VirajSanghani/vara/electronics/vara_cartridge.kicad_sch

## KiCad design electronics/vara_cartridge.kicad_sch (2026-06-03)

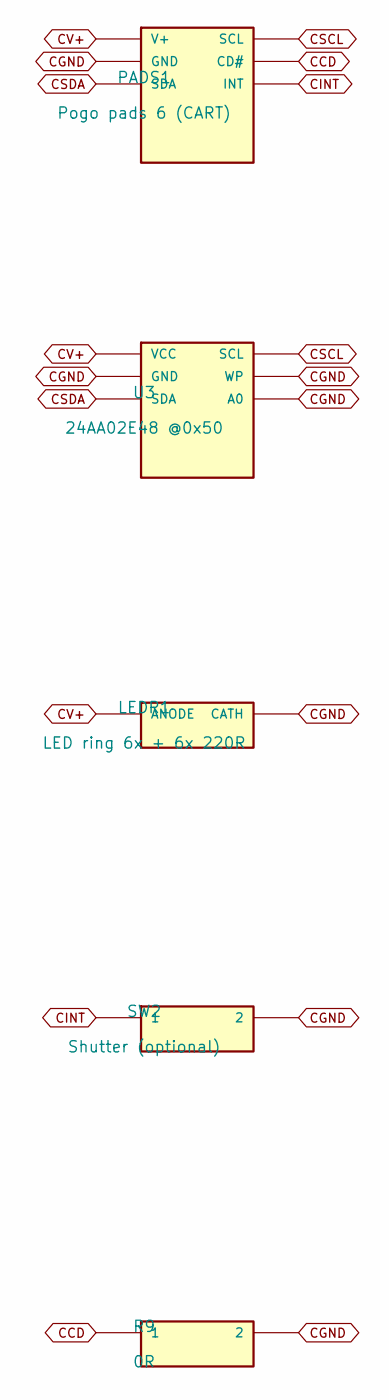
[picture p17: schematic vara_cartridge.kicad_sch]

Parts:
LEDR1: LED ring 6x + 6x 220R
PADS1: Pogo pads 6 (CART)
R9: 0R; R_0402_1005Metric
SW2: Shutter (optional)
U3: 24AA02E48 @0x50; SOT-23-6

Connections:
CCD: PADS1.5 (CD#), R9.1
CGND: LEDR1.K (CATH), PADS1.2 (GND), R9.2, SW2.2, U3.A0, U3.GND, U3.WP
CINT: PADS1.6 (INT), SW2.1
CSCL: PADS1.4 (SCL), U3.SCL
CSDA: PADS1.3 (SDA), U3.SDA
CV+: LEDR1.A (ANODE), PADS1.1 (V+), U3.VCC
