VirajSanghani/vara/electronics/vara_core.kicad_sch

## KiCad design electronics/vara_core.kicad_sch (2026-06-03)

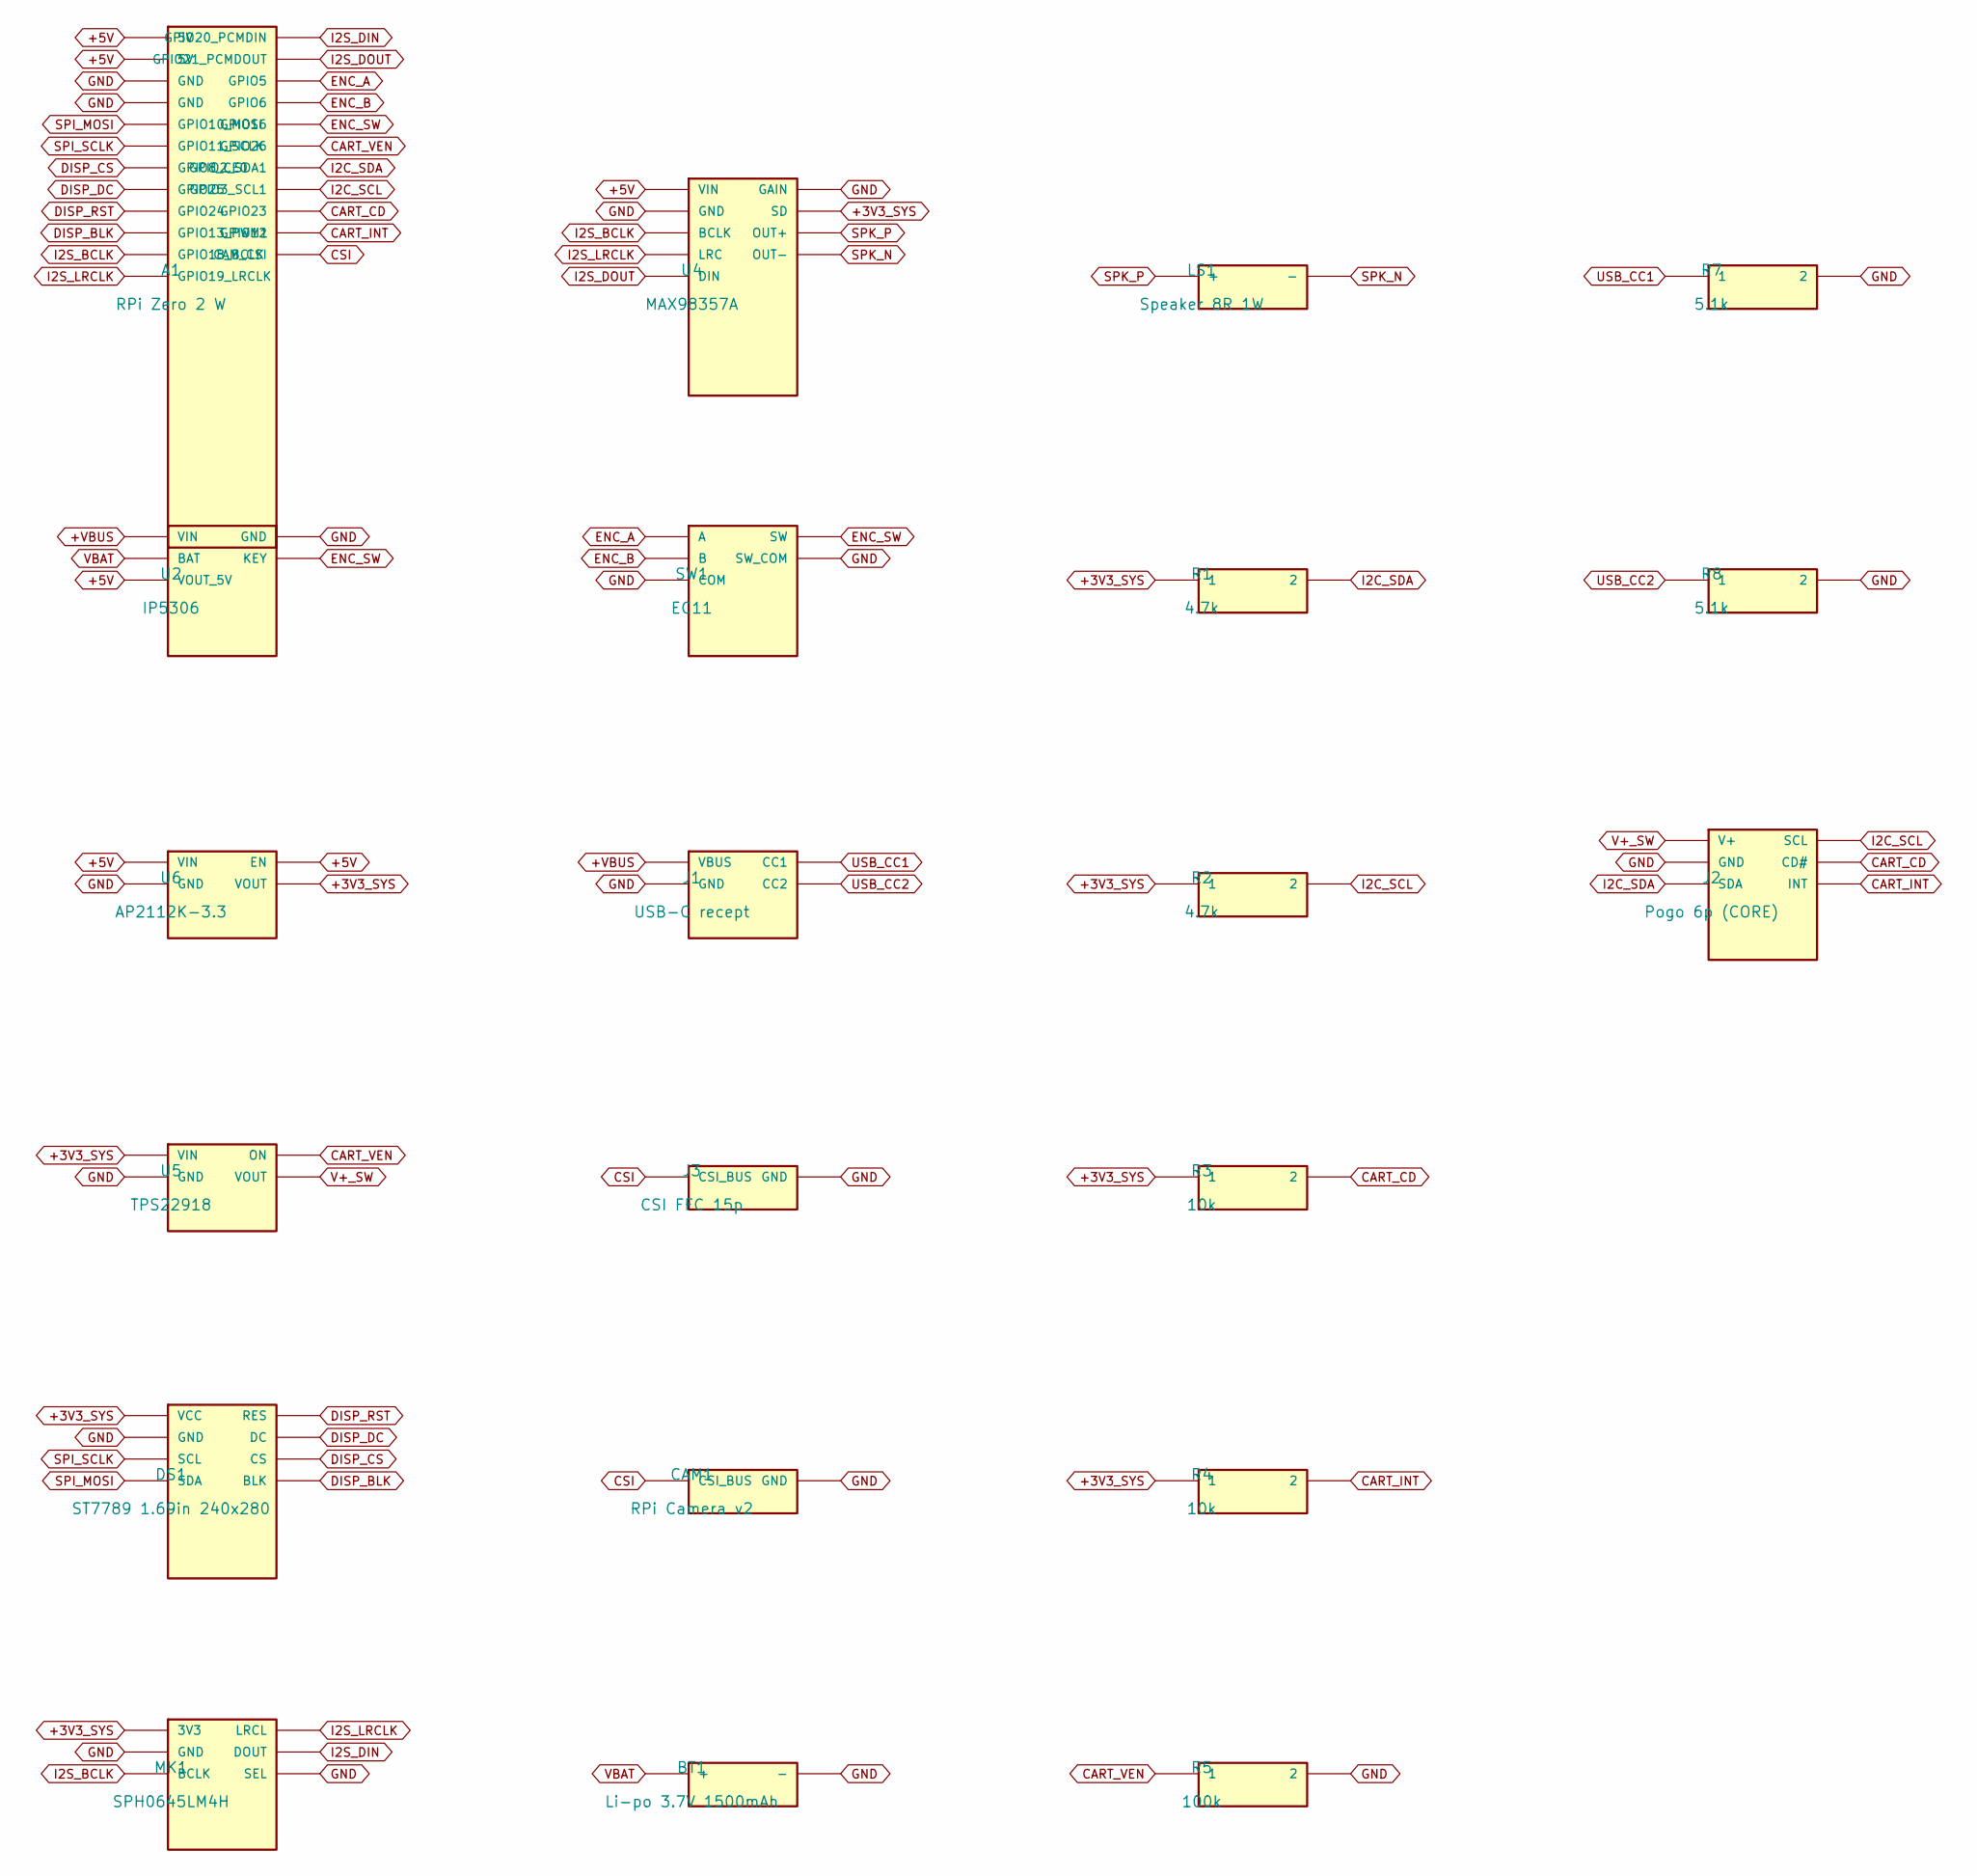
[picture p18: schematic vara_core.kicad_sch]

Parts:
A1: RPi Zero 2 W
BT1: Li-po 3.7V 1500mAh
CAM1: RPi Camera v2
DS1: ST7789 1.69in 240x280
J1: USB-C recept
J2: Pogo 6p (CORE)
J3: CSI FFC 15p
LS1: Speaker 8R 1W
MK1: SPH0645LM4H
R1, R2: 4.7k; R_0402_1005Metric
R3, R4: 10k; R_0402_1005Metric
R5: 100k; R_0402_1005Metric
R7, R8: 5.1k; R_0402_1005Metric
SW1: EC11
U2: IP5306; ESOP-8
U4: MAX98357A; QFN-16
U5: TPS22918; SOT-23-6
U6: AP2112K-3.3; SOT-23-5

Connections:
+3V3_SYS: DS1.VCC, MK1.3V3, R1.1, R2.1, R3.1, R4.1, U4.SD, U5.1 (VIN), U6.5 (VOUT)
+5V: A1.2 (5V), A1.4 (5V), U2.VOUT (VOUT_5V), U4.VIN, U6.1 (VIN), U6.3 (EN)
+VBUS: J1.VBUS, U2.VIN
CART_CD: A1.16 (GPIO23), J2.5 (CD#), R3.2
CART_INT: A1.32 (GPIO12), J2.6 (INT), R4.2
CART_VEN: A1.37 (GPIO26), R5.1, U5.3 (ON)
CSI: A1.CSI (CAM_CSI), CAM1.CSI (CSI_BUS), J3.CSI (CSI_BUS)
DISP_BLK: A1.33 (GPIO13_PWM1), DS1.BLK
DISP_CS: A1.24 (GPIO8_CE0), DS1.CS
DISP_DC: A1.22 (GPIO25), DS1.DC
DISP_RST: A1.18 (GPIO24), DS1.RES
ENC_A: A1.29 (GPIO5), SW1.A
ENC_B: A1.31 (GPIO6), SW1.B
ENC_SW: A1.36 (GPIO16), SW1.SW, U2.KEY
GND: A1.6 (GND), A1.9 (GND), BT1.-, CAM1.GND, DS1.GND, J1.GND, J2.2 (GND), J3.GND, MK1.GND, MK1.SEL, R5.2, R7.2, R8.2, SW1.C (COM), SW1.SC (SW_COM), U2.GND, U4.GAIN, U4.GND, U5.2 (GND), U6.2 (GND)
I2C_SCL: A1.5 (GPIO3_SCL1), J2.4 (SCL), R2.2
I2C_SDA: A1.3 (GPIO2_SDA1), J2.3 (SDA), R1.2
I2S_BCLK: A1.12 (GPIO18_BCLK), MK1.BCLK, U4.BCLK
I2S_DIN: A1.38 (GPIO20_PCMDIN), MK1.DOUT
I2S_DOUT: A1.40 (GPIO21_PCMDOUT), U4.DIN
I2S_LRCLK: A1.35 (GPIO19_LRCLK), MK1.LRCL, U4.LRC
SPI_MOSI: A1.19 (GPIO10_MOSI), DS1.SDA
SPI_SCLK: A1.23 (GPIO11_SCLK), DS1.SCL
SPK_N: LS1.-, U4.OUTN (OUT-)
SPK_P: LS1.+, U4.OUTP (OUT+)
USB_CC1: J1.CC1, R7.1
USB_CC2: J1.CC2, R8.1
V+_SW: J2.1 (V+), U5.4 (VOUT)
VBAT: BT1.+, U2.BAT
